MaZderMind/sweet-sixteen/3D-Renderings/sweet-sixteen-f-3d-chained.png

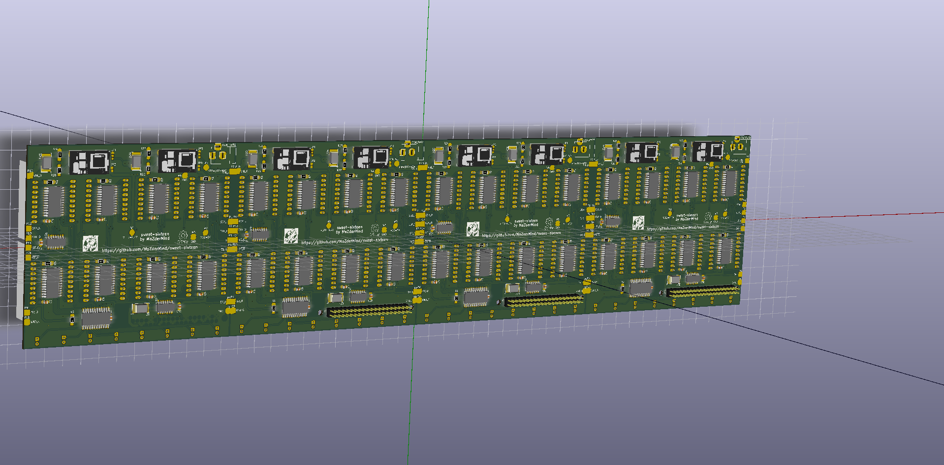
3D-Renderings/sweet-sixteen-f-3d-chained.png
